ChasParr/delwiche-sampler/pictures/IMG_1876.JPG

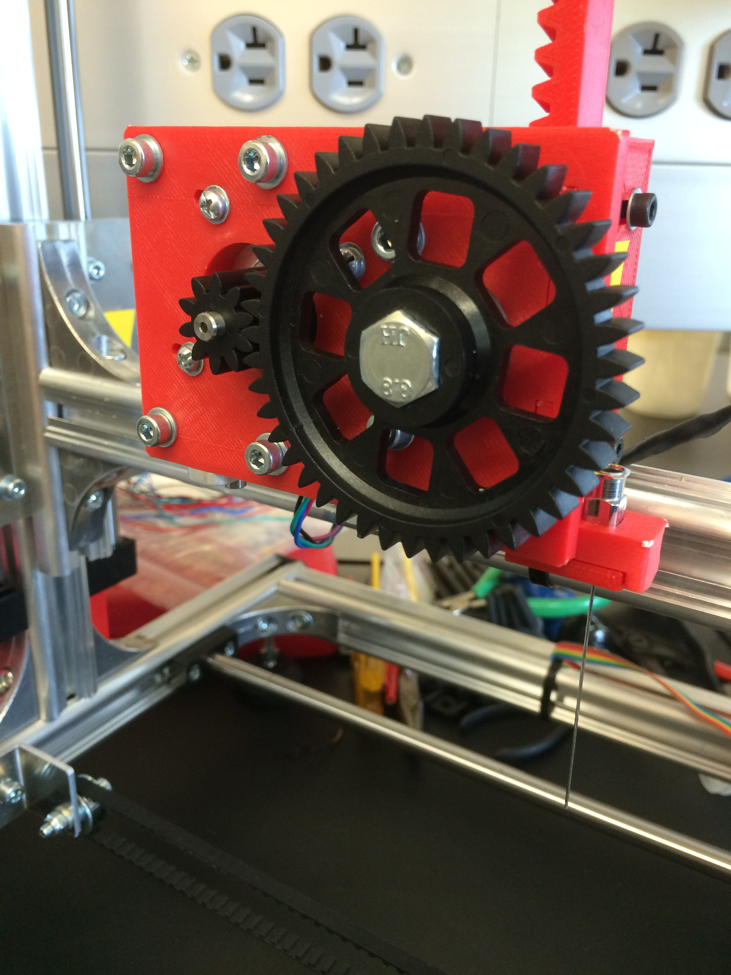
pictures/IMG_1876.JPG
