ChasParr/delwiche-sampler/pictures/IMG_1878.JPG

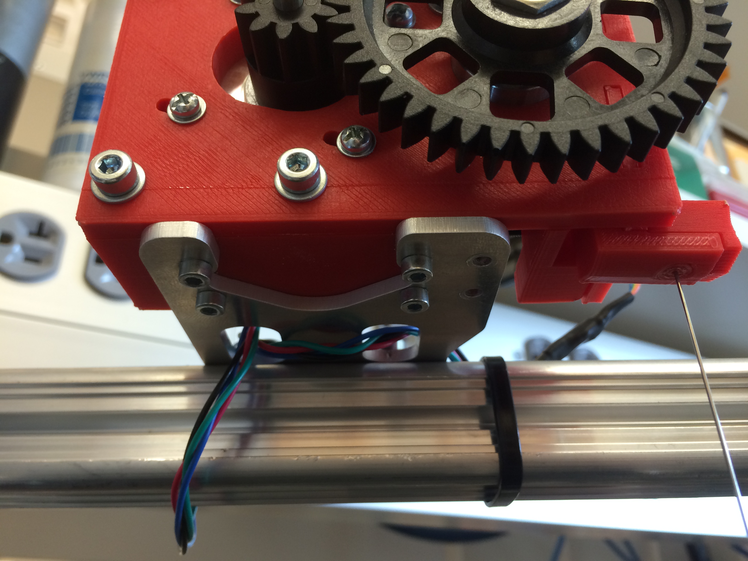
pictures/IMG_1878.JPG
