ChasParr/delwiche-sampler/pictures/IMG_1879.JPG

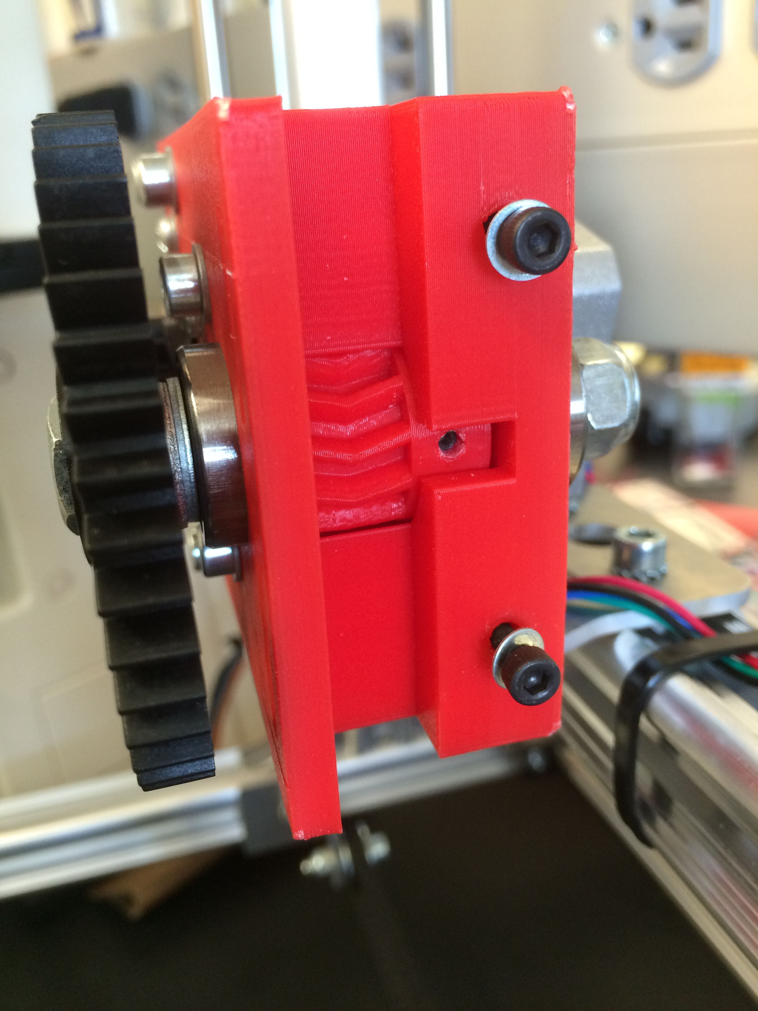
pictures/IMG_1879.JPG
